046578139/MMFT-STL/stl/gauge/MMFT_FitGauge_32x25.stl

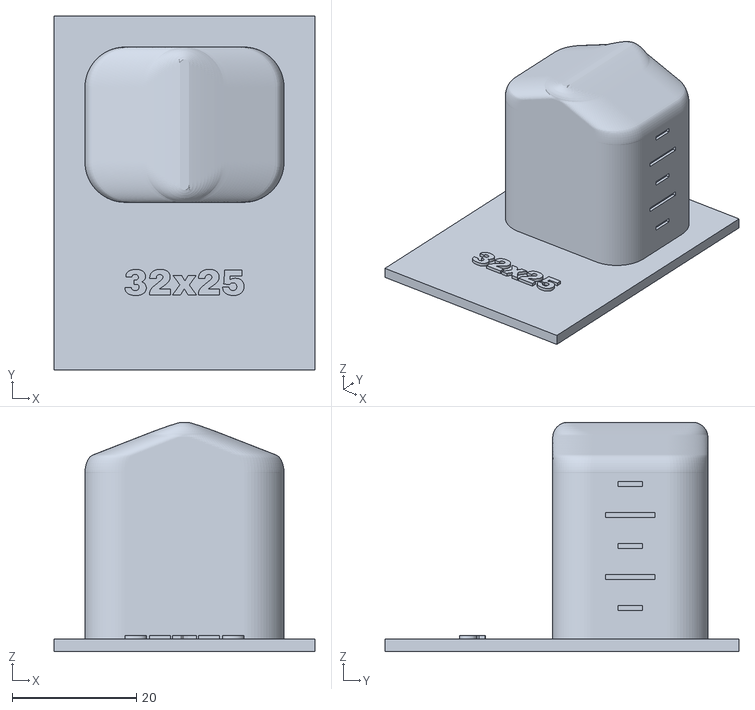
[picture p23: CAD file, 2026-09-22]
stl/gauge/MMFT_FitGauge_32x25.stl
42.0 x 57.0 x 36.9
