046578139/MMFT-STL/stl/gauge/platforms/MMFT_Fit_1911.stl

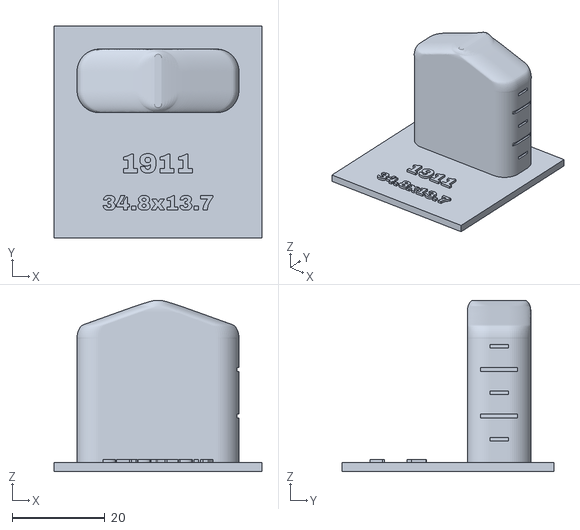
[picture p24: CAD file, 2026-09-22]
stl/gauge/platforms/MMFT_Fit_1911.stl
44.8 x 45.7 x 36.9
