046578139/MMFT-STL/stl/gauge/MMFT_FitGauge_30x19.stl

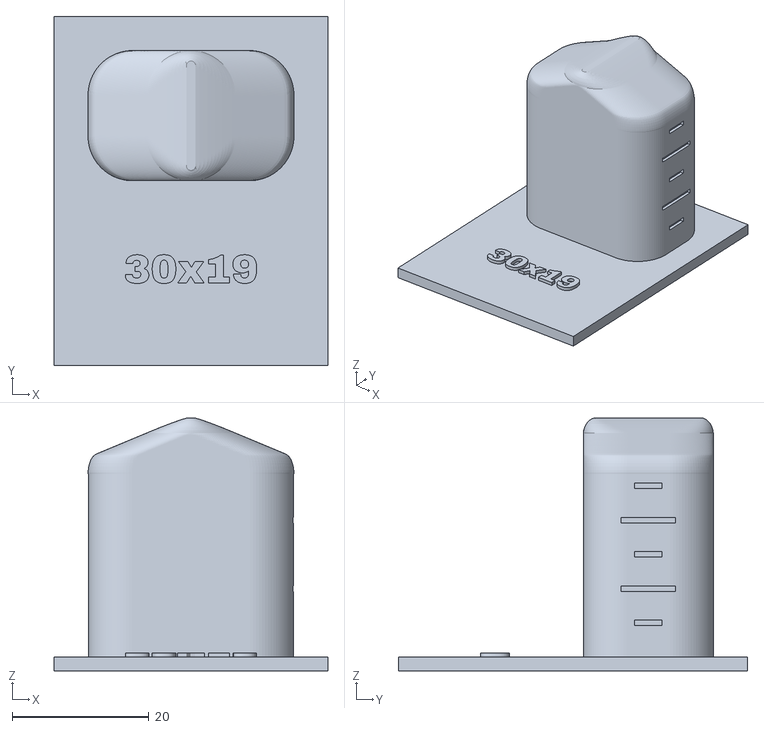
[picture p25: CAD file, 2026-09-22]
stl/gauge/MMFT_FitGauge_30x19.stl
40.0 x 51.0 x 36.9
