046578139/MMFT-STL/stl/gauge/platforms/MMFT_Fit_1911-L.stl

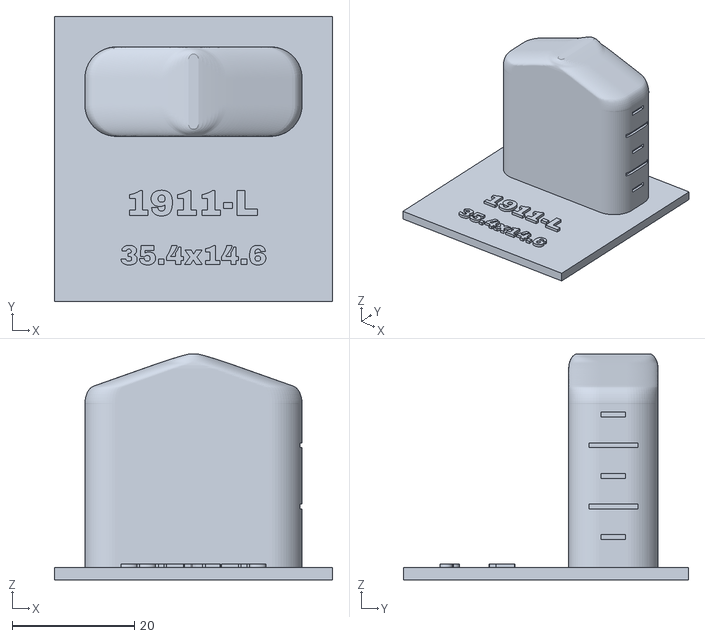
[picture p26: CAD file, 2026-09-22]
stl/gauge/platforms/MMFT_Fit_1911-L.stl
45.4 x 46.6 x 36.9
