046578139/MMFT-STL/stl/raised/MMFT_Stand_black_body.stl

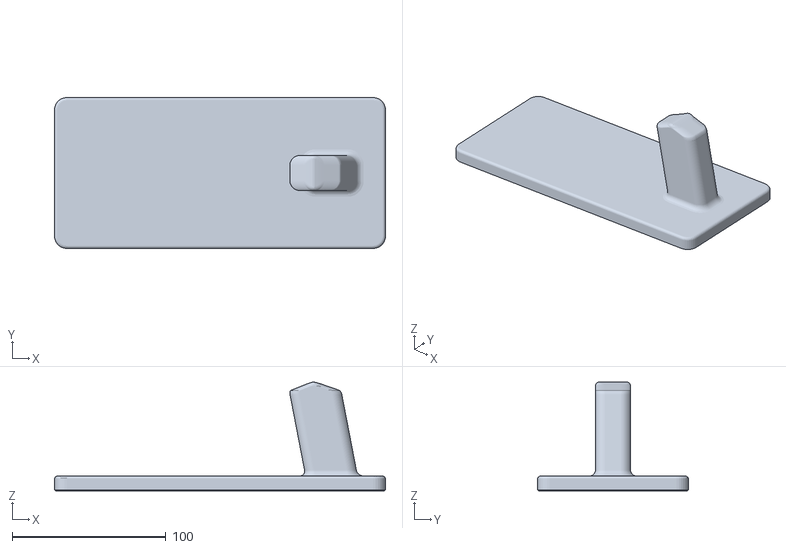
[picture p27: CAD file, 2026-09-22]
stl/raised/MMFT_Stand_black_body.stl
215.0 x 98.0 x 70.6
