046578139/MMFT-STL/stl/gauge/MMFT_FitGauge_30x25.stl

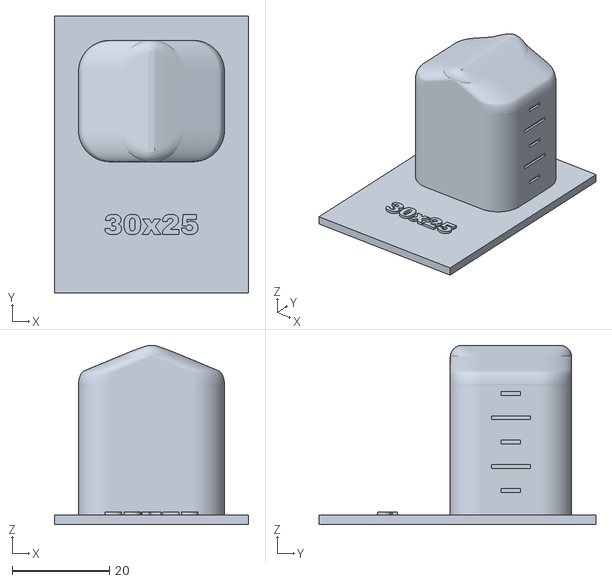
[picture p28: CAD file, 2026-09-22]
stl/gauge/MMFT_FitGauge_30x25.stl
40.0 x 57.0 x 36.9
