046578139/MMFT-STL/stl/gauge/platforms/MMFT_Fit_DS-A.stl

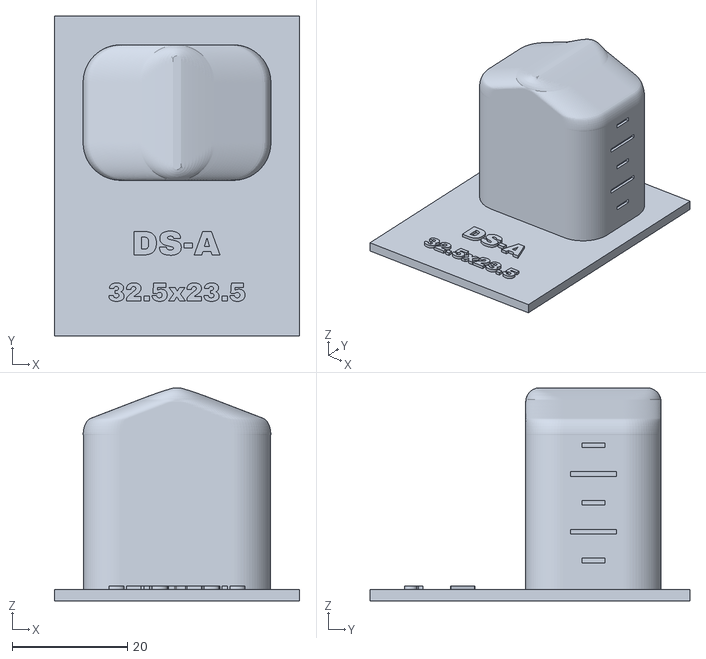
[picture p29: CAD file, 2026-09-22]
stl/gauge/platforms/MMFT_Fit_DS-A.stl
42.5 x 55.5 x 36.9
