046578139/MMFT-STL/stl/gauge/MMFT_FitGauge_34x25.stl

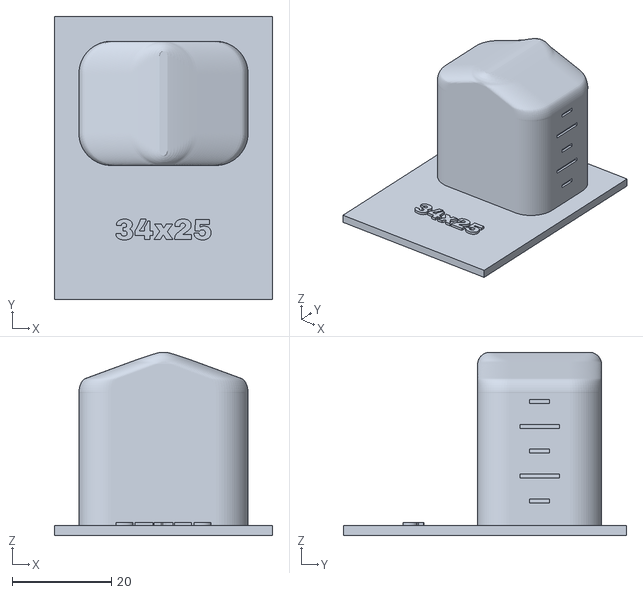
[picture p30: CAD file, 2026-09-22]
stl/gauge/MMFT_FitGauge_34x25.stl
44.0 x 57.0 x 36.9
