046578139/MMFT-STL/stl/gauge/MMFT_FitGauge_32x22.stl

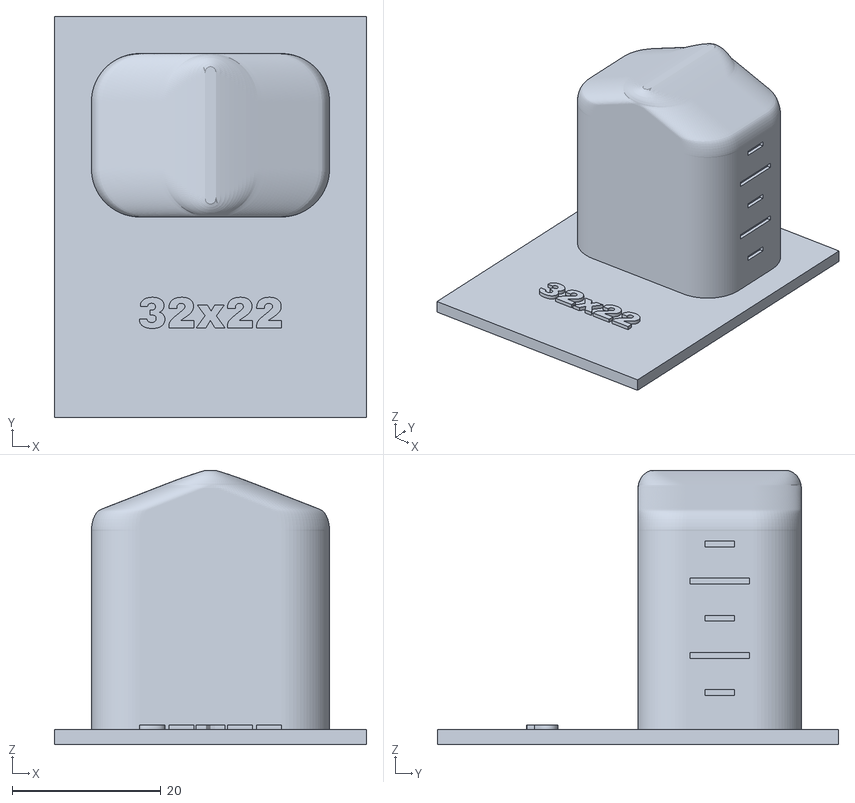
[picture p31: CAD file, 2026-09-22]
stl/gauge/MMFT_FitGauge_32x22.stl
42.0 x 54.0 x 36.9
