046578139/MMFT-STL/stl/gauge/platforms/MMFT_Fit_2011-A.stl

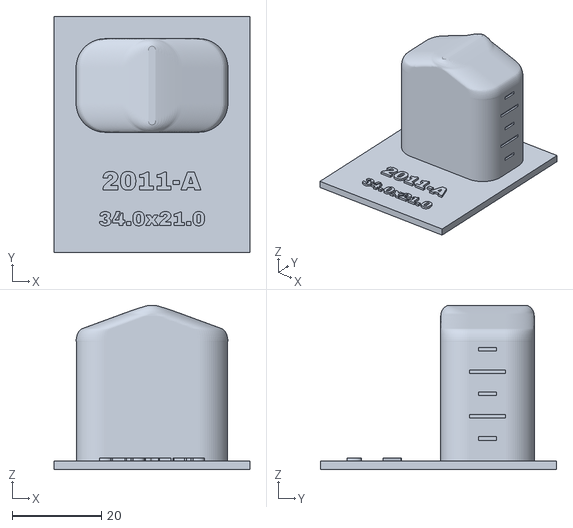
[picture p32: CAD file, 2026-09-22]
stl/gauge/platforms/MMFT_Fit_2011-A.stl
44.0 x 53.0 x 36.9
