046578139/MMFT-STL/stl/gauge/MMFT_FitGauge_34x19.stl

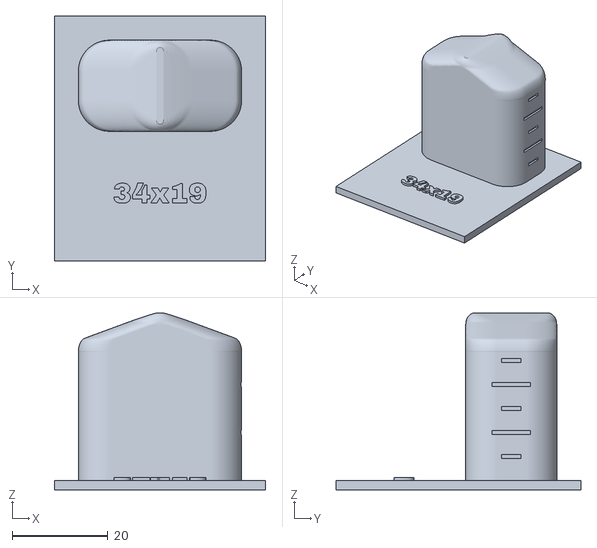
[picture p33: CAD file, 2026-09-22]
stl/gauge/MMFT_FitGauge_34x19.stl
44.0 x 51.0 x 36.9
