046578139/MMFT-STL/stl/gauge/platforms/MMFT_Fit_GLOCK.stl

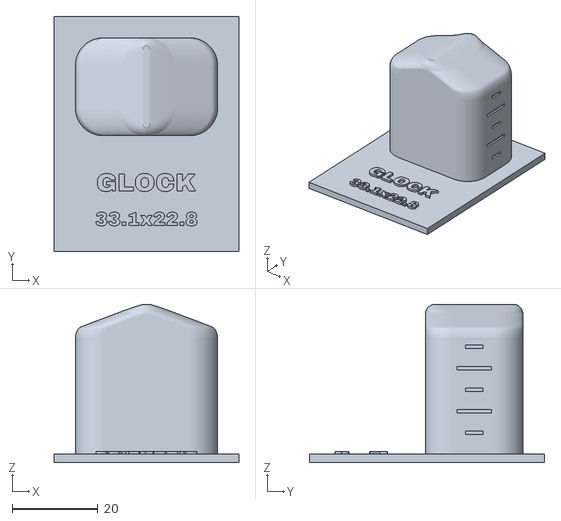
[picture p34: CAD file, 2026-09-22]
stl/gauge/platforms/MMFT_Fit_GLOCK.stl
43.1 x 54.8 x 36.9
