046578139/MMFT-STL/stl/gauge/MMFT_FitGauge_34x16.stl

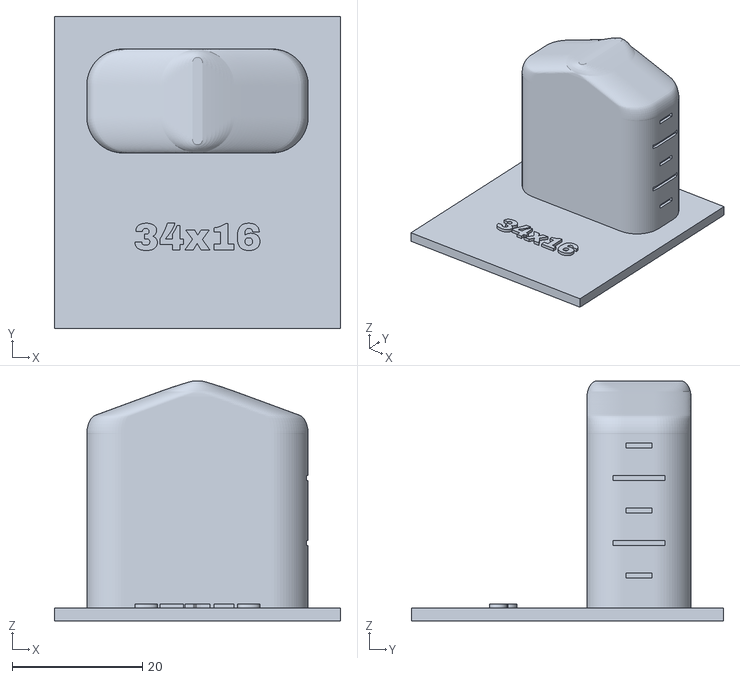
[picture p35: CAD file, 2026-09-22]
stl/gauge/MMFT_FitGauge_34x16.stl
44.0 x 48.0 x 36.9
