046578139/MMFT-STL/stl/gauge/platforms/MMFT_Fit_platforms_all.stl

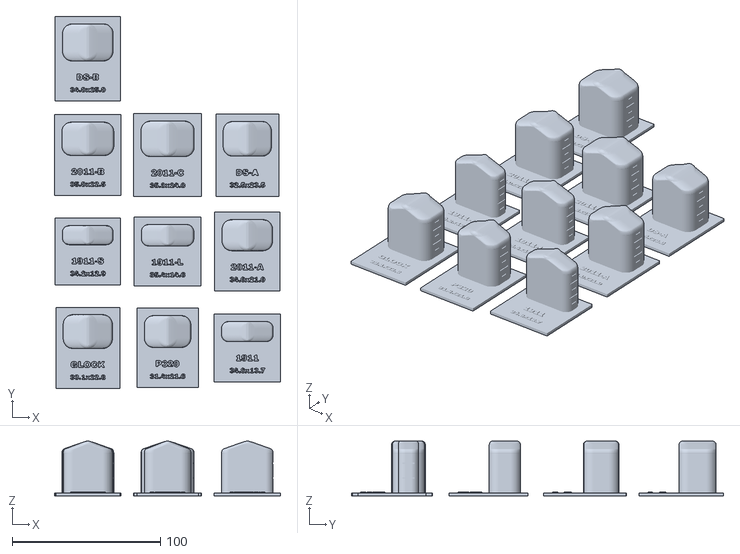
[picture p36: CAD file, 2026-09-22]
stl/gauge/platforms/MMFT_Fit_platforms_all.stl
152.5 x 250.9 x 36.9
