046578139/MMFT-STL/stl/gauge/MMFT_FitGauge_32x16.stl

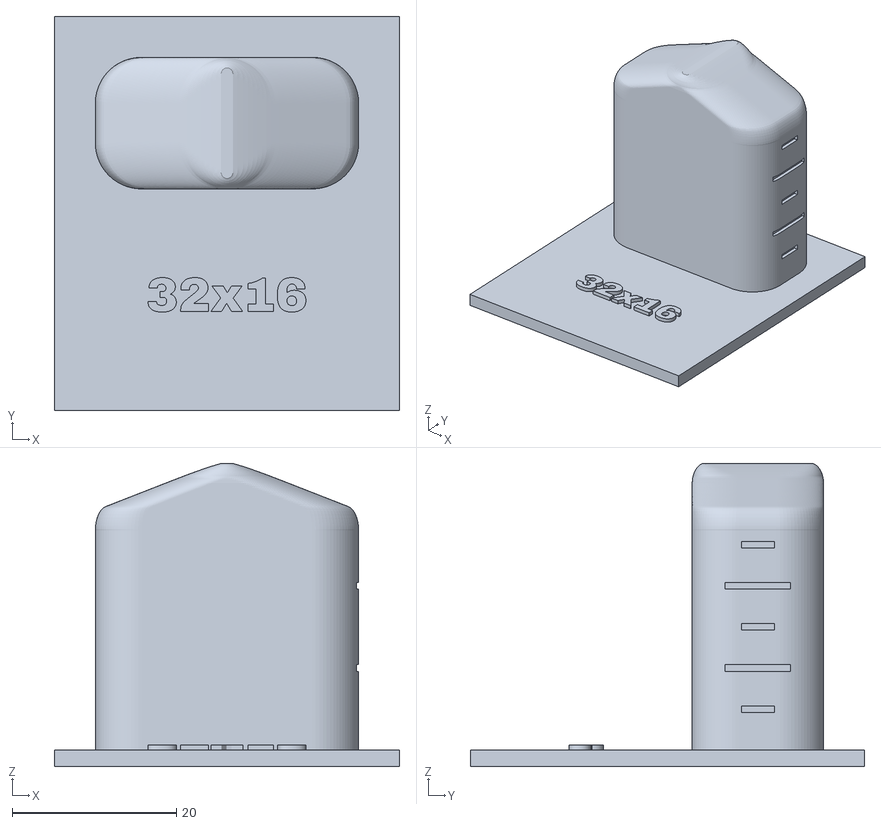
[picture p37: CAD file, 2026-09-22]
stl/gauge/MMFT_FitGauge_32x16.stl
42.0 x 48.0 x 36.9
