046578139/MMFT-STL/stl/gauge/platforms/MMFT_Fit_P320.stl

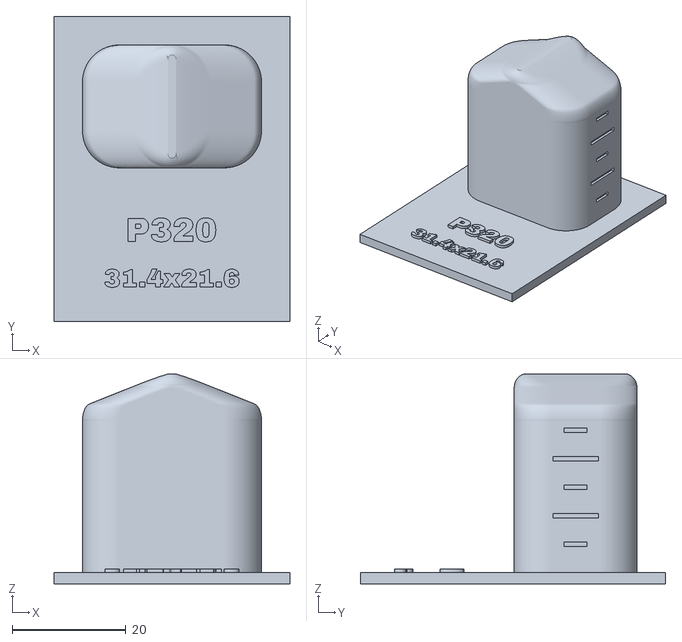
[picture p38: CAD file, 2026-09-22]
stl/gauge/platforms/MMFT_Fit_P320.stl
41.4 x 53.6 x 36.9
