046578139/MMFT-STL/stl/gauge/MMFT_FitGauge_32x19.stl

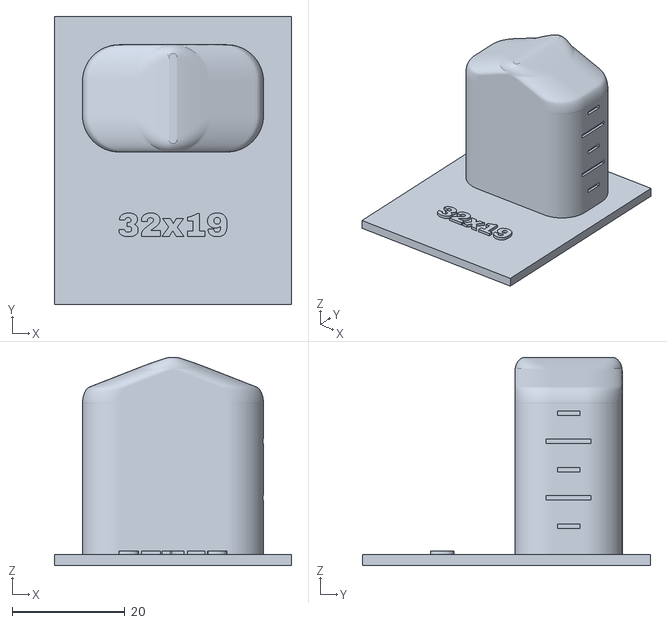
[picture p39: CAD file, 2026-09-22]
stl/gauge/MMFT_FitGauge_32x19.stl
42.0 x 51.0 x 36.9
