046578139/MMFT-STL/stl/gauge/MMFT_FitGauge_34x22.stl

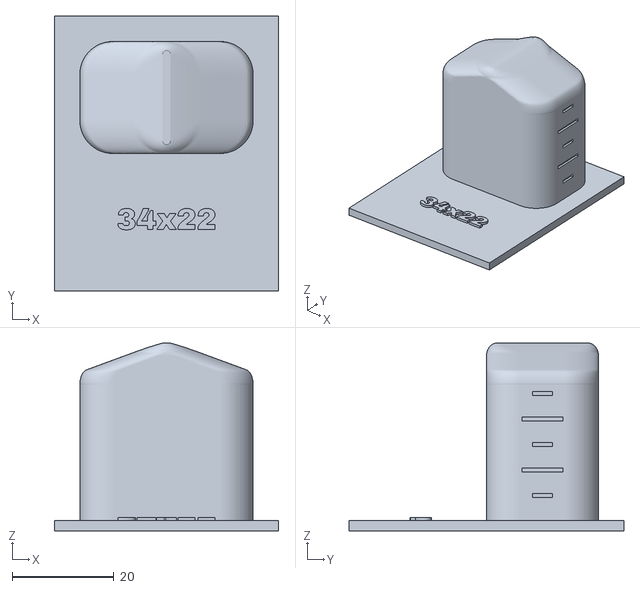
[picture p40: CAD file, 2026-09-22]
stl/gauge/MMFT_FitGauge_34x22.stl
44.0 x 54.0 x 36.9
